RingingResonance/PK232_AuxFilter/20230823_195409.jpg

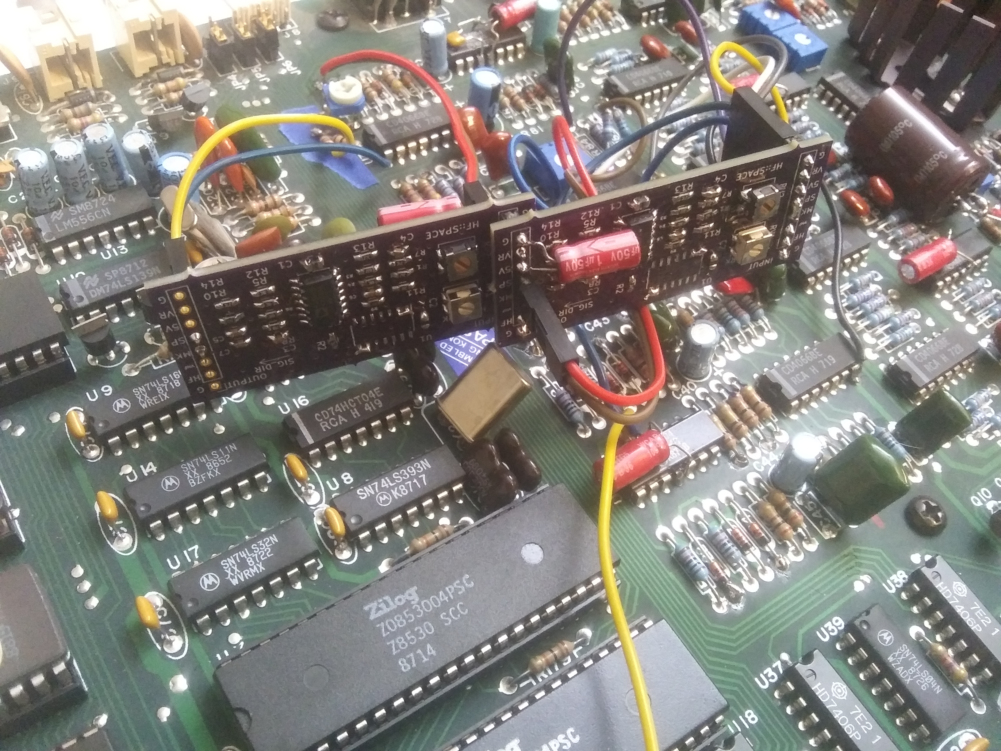
20230823_195409.jpg
